lata-mas/Monitor_co2_pistas_educativas/electric_design/pcb_jpg/ front_tracks.jpg

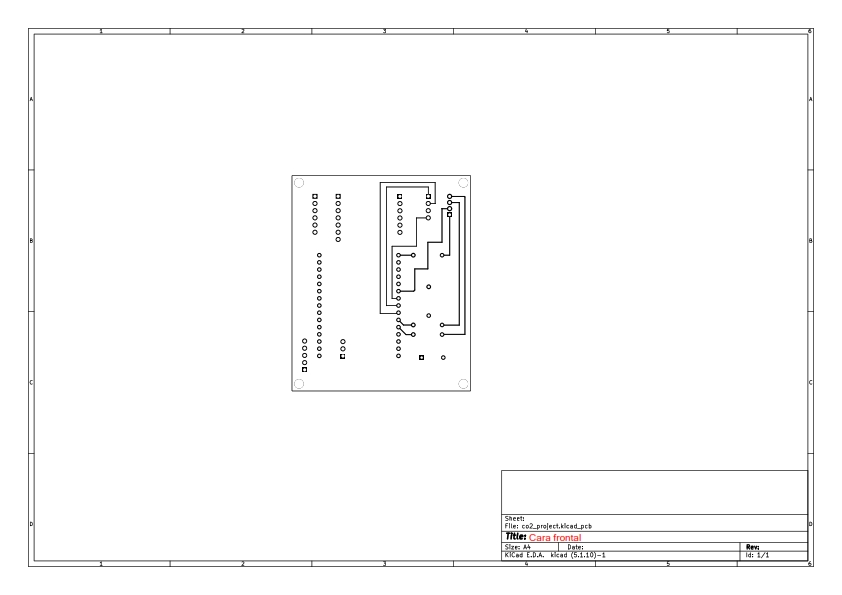
electric_design/pcb_jpg/ front_tracks.jpg
