lata-mas/Monitor_co2_pistas_educativas/software/arduino/arduino_secrets.h

#ifndef _ARDUINO_SECRETS_H_
#define _ARDUINO_SECRETS_H_

#define SECRET_SSID "YOUR-WIFI-NETWORK"
#define SECRET_PASS "YOUR-WIFI-PASSWORD"

#define SECRET_URL_PREFIX "http://iot.ier.unam.mx:8080/api/v1/"
#define SECRET_URL_POSTFIX "/telemetry"

#define SECRET_WWW_USERNAME "admin"
#define SECRET_WWW_PASSWORD "password"

#endif
